chadbailey59/CB70/Case/Choc/Choc - Left Wrist Rest.stl

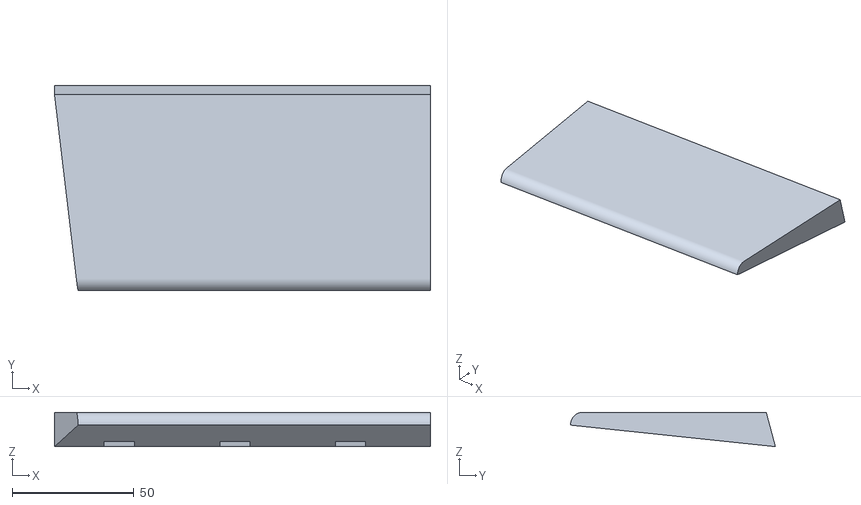
[picture p22: CAD file, 2024-07-07]
Case/Choc/Choc - Left Wrist Rest.stl
154.2 x 84.0 x 14.1
