chadbailey59/CB70/Case/MX/MX - Right Top.stl

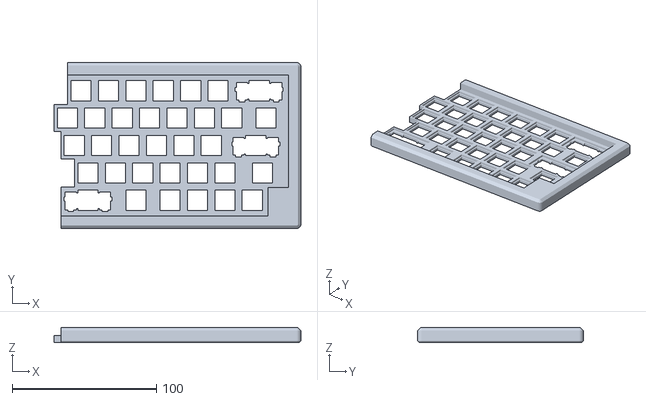
[picture p23: CAD file, 2024-07-07]
Case/MX/MX - Right Top.stl
171.3 x 115.0 x 10.2
