chadbailey59/CB70/Case/Choc/Choc - Left Top.stl

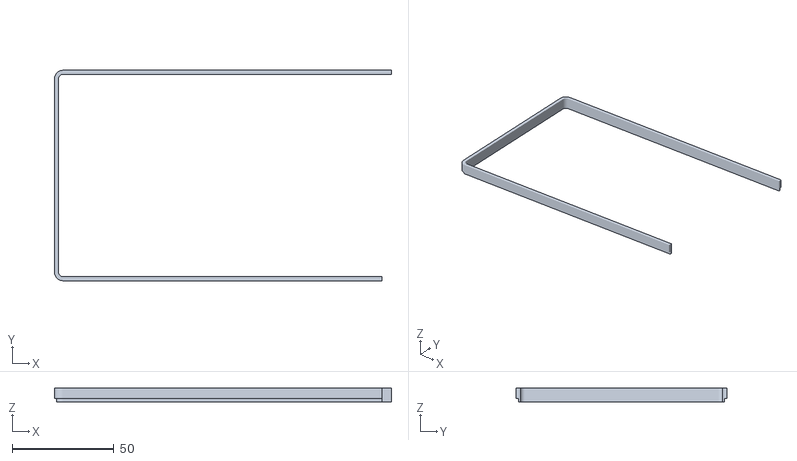
[picture p24: CAD file, 2024-07-07]
Case/Choc/Choc - Left Top.stl
165.5 x 103.4 x 6.80
