chadbailey59/CB70/Case/MX/MX - Left Wrist Rest.stl

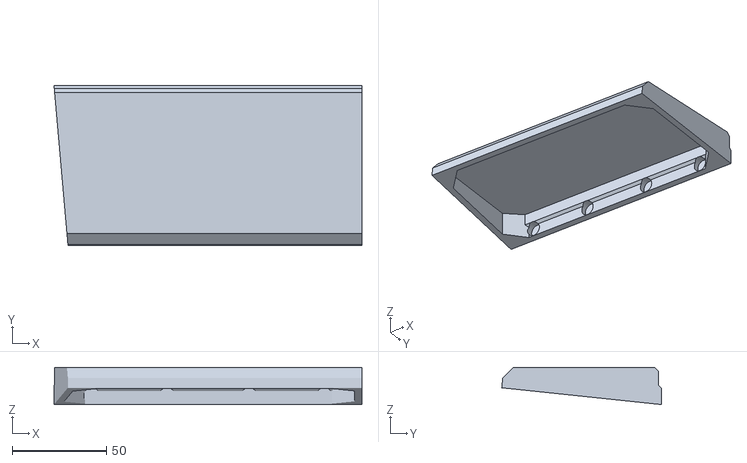
[picture p25: CAD file, 2024-07-07]
Case/MX/MX - Left Wrist Rest.stl
163.6 x 84.7 x 19.7
