chadbailey59/CB70/Case/Choc/Choc - Right Top.stl

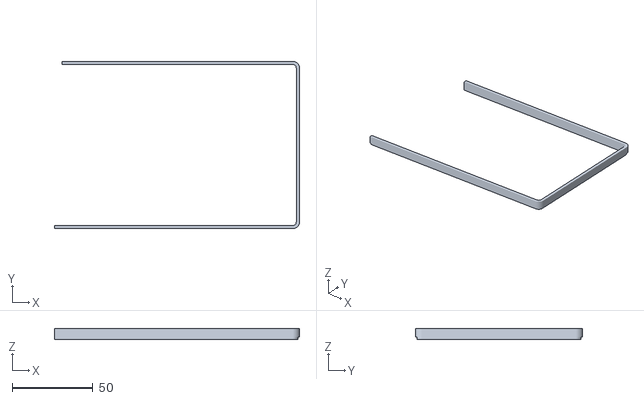
[picture p26: CAD file, 2024-07-07]
Case/Choc/Choc - Right Top.stl
151.2 x 103.4 x 6.80
