chadbailey59/CB70/Case/Choc/Choc - Right base.stl

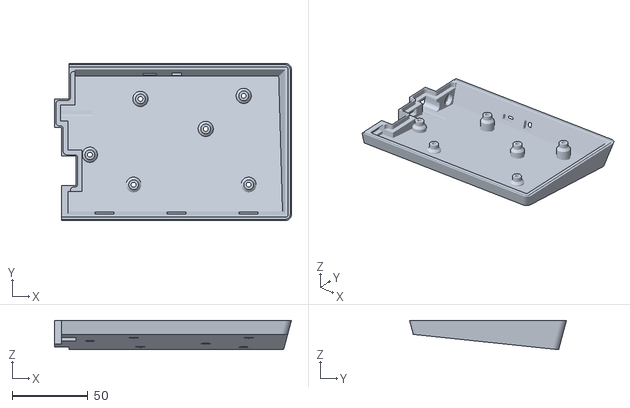
[picture p27: CAD file, 2024-07-07]
Case/Choc/Choc - Right base.stl
156.0 x 103.4 x 19.3
